seifeldaby/AC-DC-LED-Driver-PCB/images/WhatsApp Image 2026-04-27 at 10.35.28 PM (9).jpeg

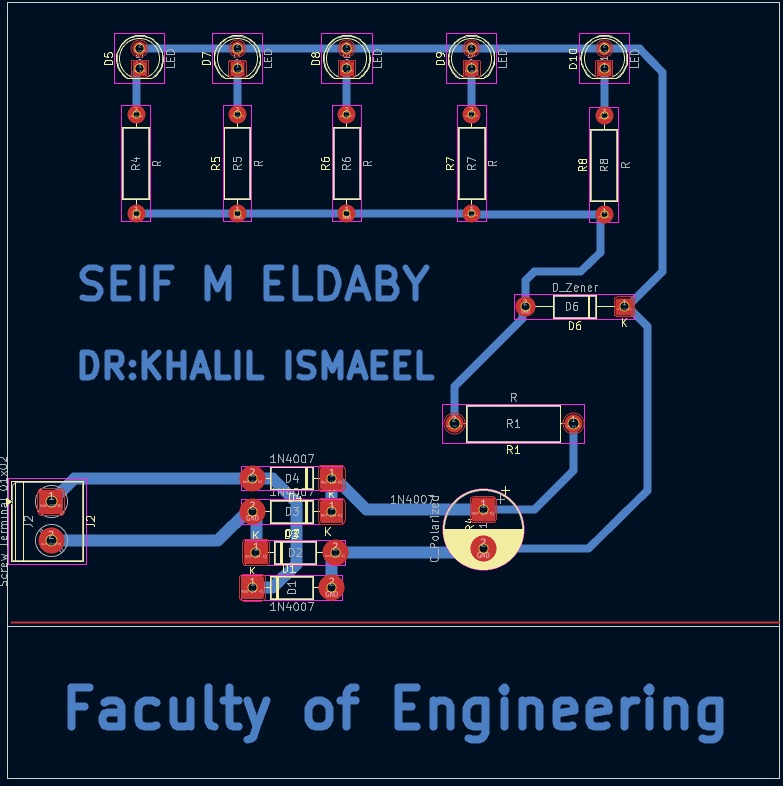
images/WhatsApp Image 2026-04-27 at 10.35.28 PM (9).jpeg
