seifeldaby/AC-DC-LED-Driver-PCB/ltspice images/power_supply_ltspice.asc

C1: cap; 2200µ; V=25
D1: diode; 1N4007
D2: diode; 1N4007
D3: diode; 1N4007
D4: diode; 1N4007
D5: zener; BZX84B9V1LY
LED1: led; QTLP690C
LED2: led; QTLP690C
LED3: led; QTLP690C
LED4: led; QTLP690C
LED5: led; QTLP690C
R1: res; 47
R2: res; 420
R3: res; 420
R4: res; 420
R5: res; 420
R6: res; 420
V1: voltage; SINE(0 17 50)
Named nets: 0
.tran 0.5
